igorlab/KH_station/PCB/img/LMC6042.jpg

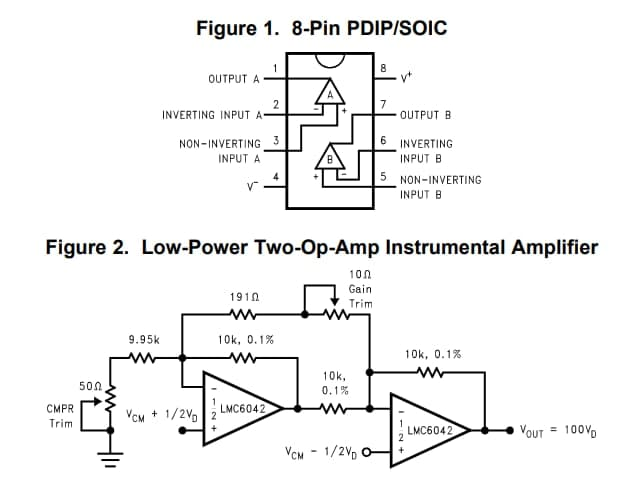
PCB/img/LMC6042.jpg
