igorlab/KH_station/STL/syringe_retainer_50ml.STL

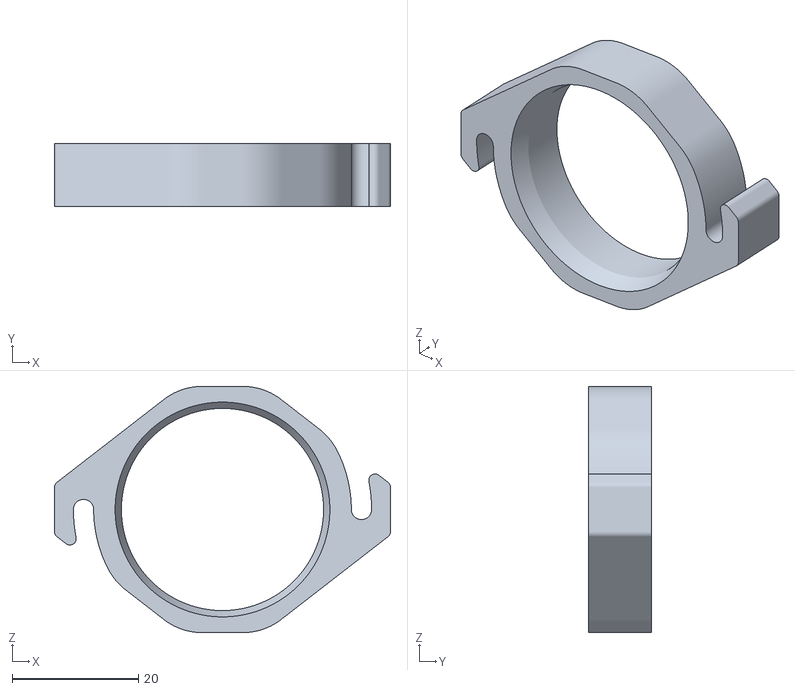
[picture p26: CAD file, 2021-12-15]
STL/syringe_retainer_50ml.STL
53.2 x 10.0 x 39.0
