igorlab/KH_station/STL/lerdge_optical_endstop_mount_v2.STL

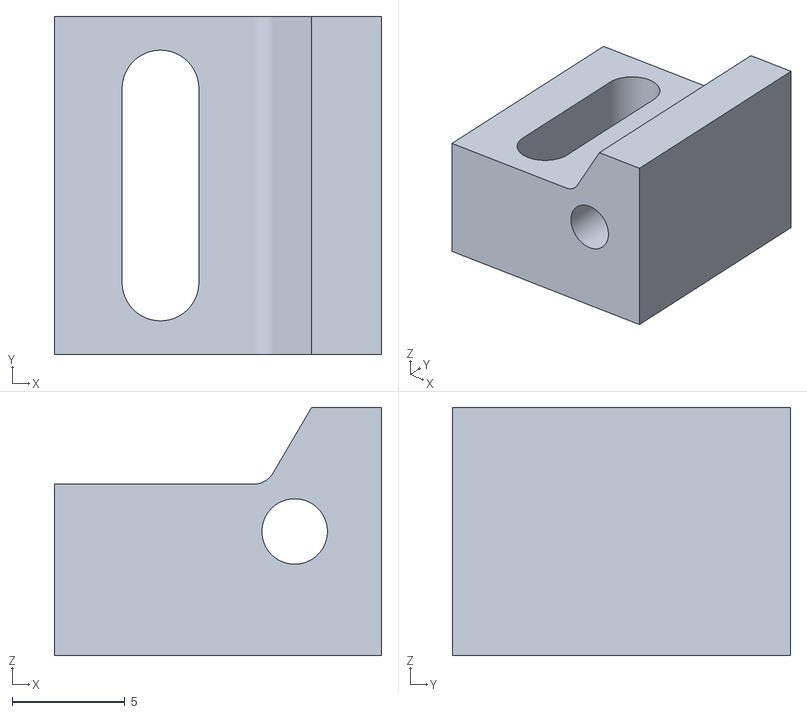
[picture p27: CAD file, 2021-12-15]
STL/lerdge_optical_endstop_mount_v2.STL
14.5 x 15.0 x 11.0
