igorlab/KH_station/Assembling/img/front1.jpg

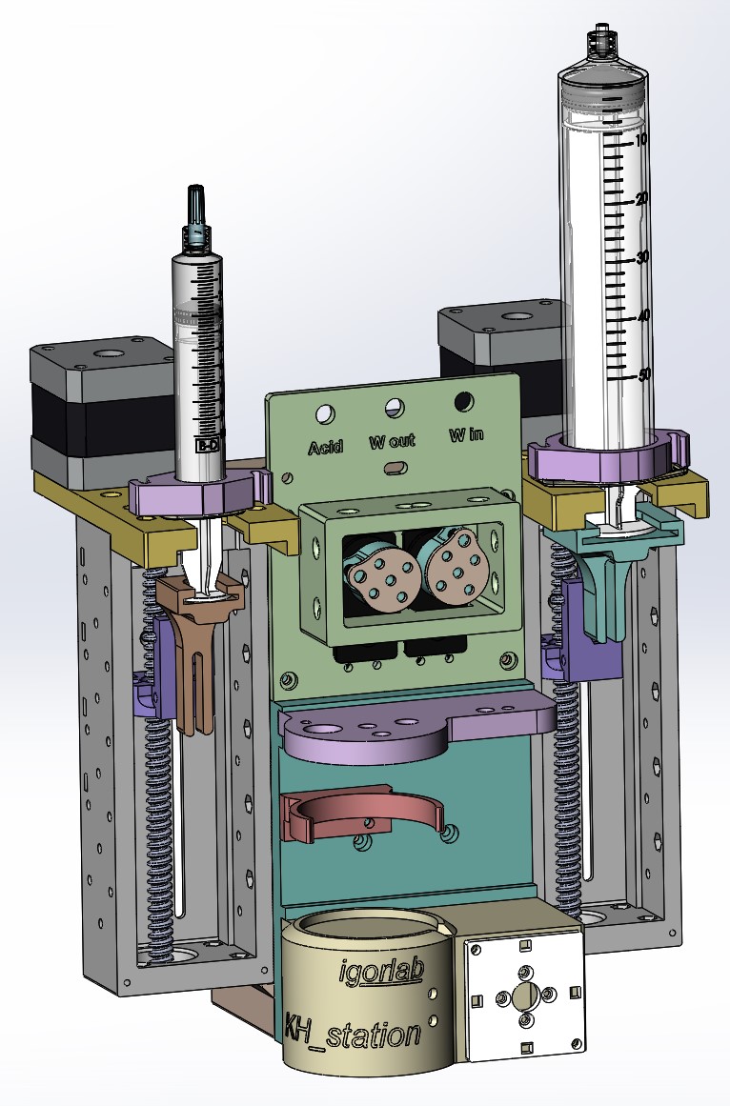
Assembling/img/front1.jpg
