igorlab/KH_station/Assembling/img/syringe_pump/5a.jpg

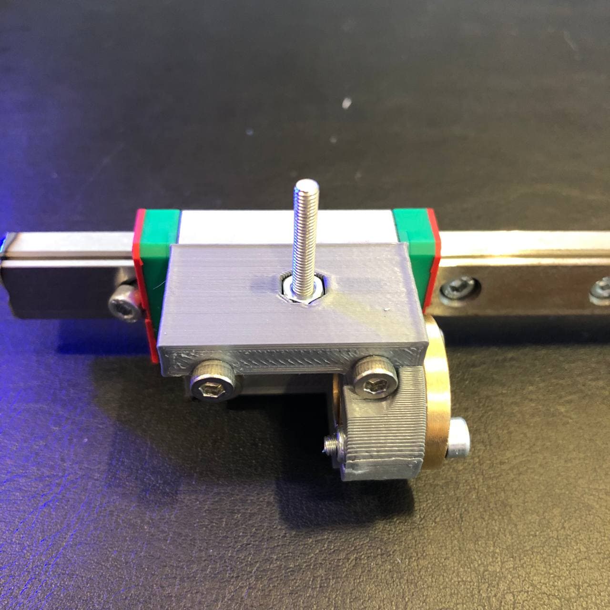
Assembling/img/syringe_pump/5a.jpg
